Slavfot/gallium-keyboard/firmware qmk/gallium/gallium.c

#include "gallium.h"

void uart_init(void) {
	SERIAL_UART_INIT();
}

void led_init(void) {
	DDRD  |= (1<<1);
	PORTD |= (1<<1);
	DDRF  |= (1<<4) | (1<<5);
	PORTF |= (1<<4) | (1<<5);
}


void matrix_init_kb(void) {
	// put your keyboard start-up code here
	// runs once when the firmware starts up
	matrix_init_user();
	uart_init();
	led_init();
}

void matrix_scan_kb(void) {
	// put your looping keyboard code here
	// runs every cycle (a lot)
	matrix_scan_user();
}

void led_set_kb(uint8_t usb_led) {

}

#ifdef ONEHAND_ENABLE
__attribute__ ((weak))
const keypos_t hand_swap_config[MATRIX_ROWS][MATRIX_COLS] = {
{{13, 0}, {12, 0}, {11, 0}, {10, 0}, {9, 0}, {8, 0}, {7, 0}, {6, 0}, {5, 0}, {4, 0}, {3, 0}, {2, 0}, {1, 0}, {0, 0}},
{{13, 1}, {12, 1}, {11, 1}, {10, 1}, {9, 1}, {8, 1}, {7, 1}, {6, 1}, {5, 1}, {4, 1}, {3, 1}, {2, 1}, {1, 1}, {0, 1}},
{{13, 2}, {12, 2}, {11, 2}, {10, 2}, {9, 2}, {8, 2}, {7, 2}, {6, 2}, {5, 2}, {4, 2}, {3, 2}, {2, 2}, {1, 2}, {0, 2}},
{{13, 3}, {12, 3}, {11, 3}, {10, 3}, {9, 3}, {8, 3}, {7, 3}, {6, 3}, {5, 3}, {4, 3}, {3, 3}, {2, 3}, {1, 3}, {0, 3}},
{{13, 4}, {12, 4}, {11, 4}, {10, 4}, {9, 4}, {8, 4}, {7, 4}, {6, 4}, {5, 4}, {4, 4}, {3, 4}, {2, 4}, {1, 4}, {0, 4}},
};
#endif
